Juerd/opentilt/color.h

struct Color {
    uint8_t r;
    uint8_t g;
    uint8_t b;
};

const Color off = { 0, 0, 0 };

/*
    perl -lane'$_ = sprintf("%d", ($_/255) ** 3 * 255) for @F[0..2]; @F==4 and
    print "const Color \L$F[3]\E = { $F[0], $F[1], $F[2] };"' /etc/X11/rgb.txt |
    grep -v tan
*/

const Color snow = { 255, 240, 240 };
const Color ghostwhite = { 234, 234, 255 };
const Color whitesmoke = { 226, 226, 226 };
const Color gainsboro = { 163, 163, 163 };
const Color floralwhite = { 255, 240, 212 };
const Color oldlace = { 249, 226, 187 };
const Color linen = { 240, 212, 187 };
const Color antiquewhite = { 240, 199, 152 };
const Color papayawhip = { 255, 209, 148 };
const Color blanchedalmond = { 255, 199, 132 };
const Color bisque = { 255, 182, 115 };
const Color peachpuff = { 255, 159, 97 };
const Color navajowhite = { 255, 168, 79 };
const Color moccasin = { 255, 182, 91 };
const Color cornsilk = { 255, 234, 163 };
const Color ivory = { 255, 255, 212 };
const Color lemonchiffon = { 255, 240, 132 };
const Color seashell = { 255, 226, 207 };
const Color honeydew = { 212, 255, 212 };
const Color mintcream = { 226, 255, 240 };
const Color azure = { 212, 255, 255 };
const Color aliceblue = { 212, 234, 255 };
const Color lavender = { 187, 187, 240 };
const Color lavenderblush = { 255, 212, 226 };
const Color mistyrose = { 255, 182, 175 };
const Color white = { 255, 255, 255 };
const Color black = { 0, 0, 0 };
const Color darkslategray = { 1, 7, 7 };
const Color darkslategrey = { 1, 7, 7 };
const Color dimgray = { 17, 17, 17 };
const Color dimgrey = { 17, 17, 17 };
const Color slategray = { 21, 32, 45 };
const Color slategrey = { 21, 32, 45 };
const Color lightslategray = { 25, 38, 55 };
const Color lightslategrey = { 25, 38, 55 };
const Color gray = { 105, 105, 105 };
const Color grey = { 105, 105, 105 };
const Color lightgrey = { 144, 144, 144 };
const Color lightgray = { 144, 144, 144 };
const Color midnightblue = { 0, 0, 21 };
const Color navy = { 0, 0, 32 };
const Color navyblue = { 0, 0, 32 };
const Color cornflowerblue = { 15, 50, 204 };
const Color darkslateblue = { 5, 3, 41 };
const Color slateblue = { 18, 11, 132 };
const Color mediumslateblue = { 28, 17, 207 };
const Color lightslateblue = { 35, 21, 255 };
const Color mediumblue = { 0, 0, 132 };
const Color royalblue = { 4, 17, 175 };
const Color blue = { 0, 0, 255 };
const Color dodgerblue = { 0, 45, 255 };
const Color deepskyblue = { 0, 107, 255 };
const Color skyblue = { 37, 134, 199 };
const Color lightskyblue = { 37, 134, 240 };
const Color steelblue = { 5, 33, 89 };
const Color lightsteelblue = { 83, 115, 168 };
const Color lightblue = { 79, 154, 187 };
const Color powderblue = { 83, 172, 187 };
const Color paleturquoise = { 82, 207, 207 };
const Color darkturquoise = { 0, 134, 140 };
const Color mediumturquoise = { 5, 140, 130 };
const Color turquoise = { 4, 172, 138 };
const Color cyan = { 0, 255, 255 };
const Color lightcyan = { 172, 255, 255 };
const Color cadetblue = { 13, 60, 62 };
const Color mediumaquamarine = { 16, 132, 75 };
const Color aquamarine = { 31, 255, 146 };
const Color darkgreen = { 0, 15, 0 };
const Color darkolivegreen = { 9, 18, 1 };
const Color darkseagreen = { 44, 102, 44 };
const Color seagreen = { 1, 41, 10 };
const Color mediumseagreen = { 3, 88, 22 };
const Color lightseagreen = { 0, 86, 75 };
const Color palegreen = { 54, 243, 54 };
const Color springgreen = { 0, 255, 31 };
const Color lawngreen = { 29, 246, 0 };
const Color green = { 0, 255, 0 };
const Color chartreuse = { 31, 255, 0 };
const Color mediumspringgreen = { 0, 240, 56 };
const Color greenyellow = { 79, 255, 1 };
const Color limegreen = { 1, 132, 1 };
const Color yellowgreen = { 56, 132, 1 };
const Color forestgreen = { 0, 41, 0 };
const Color olivedrab = { 18, 44, 0 };
const Color darkkhaki = { 103, 94, 18 };
const Color khaki = { 212, 187, 42 };
const Color palegoldenrod = { 207, 192, 75 };
const Color lightgoldenrodyellow = { 240, 240, 142 };
const Color lightyellow = { 255, 255, 172 };
const Color yellow = { 255, 255, 0 };
const Color gold = { 255, 152, 0 };
const Color lightgoldenrod = { 207, 165, 33 };
const Color goldenrod = { 159, 69, 0 };
const Color darkgoldenrod = { 95, 37, 0 };
const Color rosybrown = { 102, 44, 44 };
const Color indianred = { 132, 11, 11 };
const Color saddlebrown = { 41, 5, 0 };
const Color sienna = { 62, 8, 1 };
const Color peru = { 132, 36, 3 };
const Color burlywood = { 168, 95, 37 };
const Color beige = { 226, 226, 163 };
const Color wheat = { 226, 168, 88 };
const Color sandybrown = { 223, 67, 13 };
const Color chocolate = { 142, 17, 0 };
const Color firebrick = { 86, 0, 0 };
const Color brown = { 69, 1, 1 };
const Color darksalmon = { 194, 51, 27 };
const Color salmon = { 240, 32, 22 };
const Color lightsalmon = { 255, 62, 27 };
const Color orange = { 255, 69, 0 };
const Color darkorange = { 255, 42, 0 };
const Color coral = { 255, 31, 7 };
const Color lightcoral = { 212, 32, 32 };
const Color tomato = { 255, 14, 5 };
const Color orangered = { 255, 5, 0 };
const Color red = { 255, 0, 0 };
const Color hotpink = { 255, 17, 89 };
const Color deeppink = { 255, 0, 48 };
const Color pink = { 255, 108, 128 };
const Color lightpink = { 255, 92, 110 };
const Color palevioletred = { 161, 21, 48 };
const Color maroon = { 83, 1, 13 };
const Color mediumvioletred = { 121, 0, 36 };
const Color violetred = { 138, 0, 45 };
const Color magenta = { 255, 0, 255 };
const Color violet = { 207, 33, 207 };
const Color plum = { 165, 62, 165 };
const Color orchid = { 159, 21, 150 };
const Color mediumorchid = { 98, 9, 144 };
const Color darkorchid = { 55, 1, 130 };
const Color darkviolet = { 49, 0, 144 };
const Color blueviolet = { 40, 1, 177 };
const Color purple = { 62, 0, 212 };
const Color mediumpurple = { 48, 21, 161 };
const Color thistle = { 154, 107, 154 };
const Color snow1 = { 255, 240, 240 };
const Color snow2 = { 207, 194, 194 };
const Color snow3 = { 132, 124, 124 };
const Color snow4 = { 41, 39, 39 };
const Color seashell1 = { 255, 226, 207 };
const Color seashell2 = { 207, 184, 168 };
const Color seashell3 = { 132, 117, 107 };
const Color seashell4 = { 41, 37, 33 };
const Color antiquewhite1 = { 255, 209, 161 };
const Color antiquewhite2 = { 207, 170, 130 };
const Color antiquewhite3 = { 132, 108, 83 };
const Color antiquewhite4 = { 41, 34, 26 };
const Color bisque1 = { 255, 182, 115 };
const Color bisque2 = { 207, 148, 94 };
const Color bisque3 = { 132, 94, 60 };
const Color bisque4 = { 41, 30, 18 };
const Color peachpuff1 = { 255, 159, 97 };
const Color peachpuff2 = { 207, 128, 79 };
const Color peachpuff3 = { 132, 82, 50 };
const Color peachpuff4 = { 41, 25, 15 };
const Color navajowhite1 = { 255, 168, 79 };
const Color navajowhite2 = { 207, 136, 64 };
const Color navajowhite3 = { 132, 88, 41 };
const Color navajowhite4 = { 41, 27, 12 };
const Color lemonchiffon1 = { 255, 240, 132 };
const Color lemonchiffon2 = { 207, 194, 107 };
const Color lemonchiffon3 = { 132, 124, 69 };
const Color lemonchiffon4 = { 41, 39, 21 };
const Color cornsilk1 = { 255, 234, 163 };
const Color cornsilk2 = { 207, 192, 132 };
const Color cornsilk3 = { 132, 123, 85 };
const Color cornsilk4 = { 41, 38, 26 };
const Color ivory1 = { 255, 255, 212 };
const Color ivory2 = { 207, 207, 172 };
const Color ivory3 = { 132, 132, 110 };
const Color ivory4 = { 41, 41, 34 };
const Color honeydew1 = { 212, 255, 212 };
const Color honeydew2 = { 172, 207, 172 };
const Color honeydew3 = { 110, 132, 110 };
const Color honeydew4 = { 34, 41, 34 };
const Color lavenderblush1 = { 255, 212, 226 };
const Color lavenderblush2 = { 207, 172, 184 };
const Color lavenderblush3 = { 132, 110, 117 };
const Color lavenderblush4 = { 41, 34, 37 };
const Color mistyrose1 = { 255, 182, 175 };
const Color mistyrose2 = { 207, 148, 142 };
const Color mistyrose3 = { 132, 94, 91 };
const Color mistyrose4 = { 41, 30, 28 };
const Color azure1 = { 212, 255, 255 };
const Color azure2 = { 172, 207, 207 };
const Color azure3 = { 110, 132, 132 };
const Color azure4 = { 34, 41, 41 };
const Color slateblue1 = { 34, 21, 255 };
const Color slateblue2 = { 27, 16, 207 };
const Color slateblue3 = { 17, 10, 132 };
const Color slateblue4 = { 5, 3, 41 };
const Color royalblue1 = { 5, 25, 255 };
const Color royalblue2 = { 4, 20, 207 };
const Color royalblue3 = { 3, 13, 132 };
const Color royalblue4 = { 0, 4, 41 };
const Color blue1 = { 0, 0, 255 };
const Color blue2 = { 0, 0, 207 };
const Color blue3 = { 0, 0, 132 };
const Color blue4 = { 0, 0, 41 };
const Color dodgerblue1 = { 0, 45, 255 };
const Color dodgerblue2 = { 0, 37, 207 };
const Color dodgerblue3 = { 0, 24, 132 };
const Color dodgerblue4 = { 0, 7, 41 };
const Color steelblue1 = { 14, 95, 255 };
const Color steelblue2 = { 11, 78, 207 };
const Color steelblue3 = { 7, 49, 132 };
const Color steelblue4 = { 2, 15, 41 };
const Color deepskyblue1 = { 0, 107, 255 };
const Color deepskyblue2 = { 0, 86, 207 };
const Color deepskyblue3 = { 0, 56, 132 };
const Color deepskyblue4 = { 0, 17, 41 };
const Color skyblue1 = { 37, 134, 255 };
const Color skyblue2 = { 30, 108, 207 };
const Color skyblue3 = { 19, 70, 132 };
const Color skyblue4 = { 6, 21, 41 };
const Color lightskyblue1 = { 83, 177, 255 };
const Color lightskyblue2 = { 67, 144, 207 };
const Color lightskyblue3 = { 43, 92, 132 };
const Color lightskyblue4 = { 13, 28, 41 };
const Color slategray1 = { 119, 177, 255 };
const Color slategray2 = { 97, 144, 207 };
const Color slategray3 = { 61, 92, 132 };
const Color slategray4 = { 19, 28, 41 };
const Color lightsteelblue1 = { 126, 175, 255 };
const Color lightsteelblue2 = { 102, 142, 207 };
const Color lightsteelblue3 = { 65, 91, 132 };
const Color lightsteelblue4 = { 20, 28, 41 };
const Color lightblue1 = { 107, 209, 255 };
const Color lightblue2 = { 86, 170, 207 };
const Color lightblue3 = { 56, 108, 132 };
const Color lightblue4 = { 17, 34, 41 };
const Color lightcyan1 = { 172, 255, 255 };
const Color lightcyan2 = { 140, 207, 207 };
const Color lightcyan3 = { 89, 132, 132 };
const Color lightcyan4 = { 27, 41, 41 };
const Color paleturquoise1 = { 100, 255, 255 };
const Color paleturquoise2 = { 81, 207, 207 };
const Color paleturquoise3 = { 51, 132, 132 };
const Color paleturquoise4 = { 16, 41, 41 };
const Color cadetblue1 = { 54, 226, 255 };
const Color cadetblue2 = { 44, 184, 207 };
const Color cadetblue3 = { 27, 117, 132 };
const Color cadetblue4 = { 8, 37, 41 };
const Color turquoise1 = { 0, 226, 255 };
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
const Color darkgrey = { 74, 74, 74 };
const Color darkgray = { 74, 74, 74 };
const Color darkblue = { 0, 0, 41 };
const Color darkcyan = { 0, 41, 41 };
const Color darkmagenta = { 41, 0, 41 };
const Color darkred = { 41, 0, 0 };
const Color lightgreen = { 45, 207, 45 };
