Juerd/opentilt/shiv.h

/* Inspired by
   http://openenergymonitor.org/emon/sites/default/files/GLCD_SSM.ino
*/

#ifndef sleep_bod_disable // not present in old versions of AVR toolset.
#define sleep_bod_disable() \
do { \
  uint8_t tempreg; \
  __asm__ __volatile__("in %[tempreg], %[mcucr]" "\n\t" \
                       "ori %[tempreg], %[bods_bodse]" "\n\t" \
                       "out %[mcucr], %[tempreg]" "\n\t" \
                       "andi %[tempreg], %[not_bodse]" "\n\t" \
                       "out %[mcucr], %[tempreg]" \
                       : [tempreg] "=&d" (tempreg) \
                       : [mcucr] "I" _SFR_IO_ADDR(MCUCR), \
                         [bods_bodse] "i" (_BV(BODS) | _BV(BODSE)), \
                         [not_bodse] "i" (~_BV(BODSE))); \
} while (0)
#endif
